jeffThompson/VibrationInterface/ProcessPhotos/2ChannelVibeBoard_Back.jpg

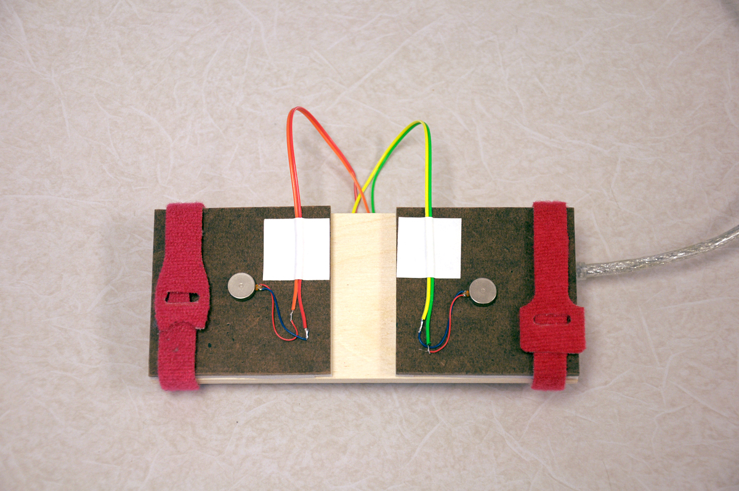
ProcessPhotos/2ChannelVibeBoard_Back.jpg
