jeffThompson/VibrationInterface/ProcessPhotos/2ChannelVibeBoard_Front.jpg

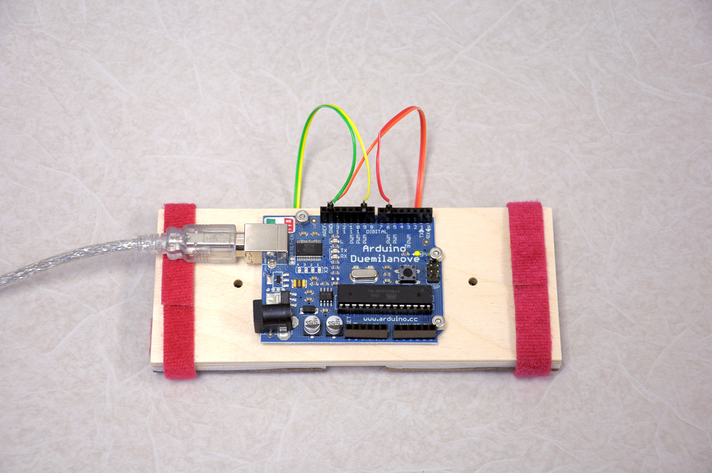
ProcessPhotos/2ChannelVibeBoard_Front.jpg
