jeffThompson/VibrationInterface/ProcessPhotos/2dArrayGeneration_Arduino-web.png

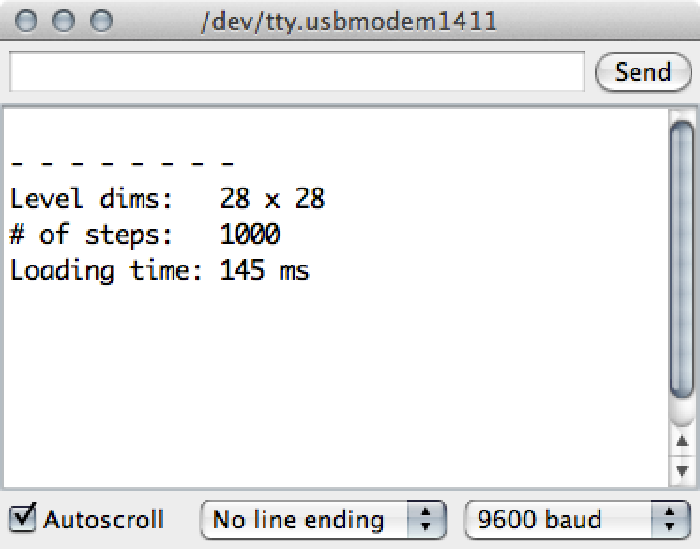
ProcessPhotos/2dArrayGeneration_Arduino-web.png
