jeffThompson/VibrationInterface/ProcessPhotos/Black1-4inBoard.jpg

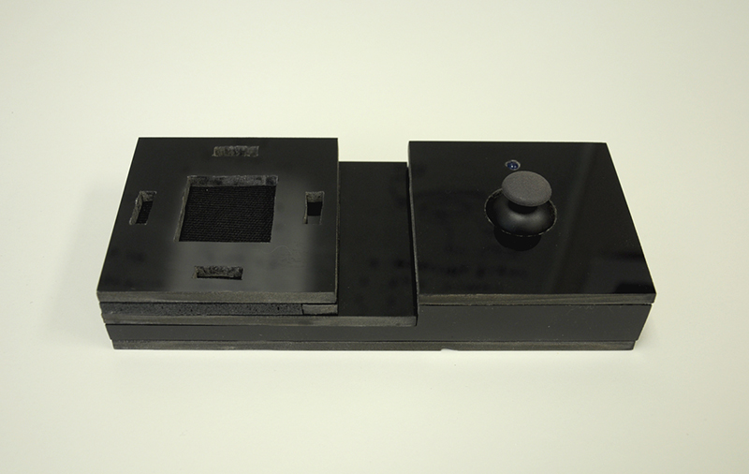
ProcessPhotos/Black1-4inBoard.jpg
