jeffThompson/VibrationInterface/ProcessPhotos/Board_v0.9Bottom.png

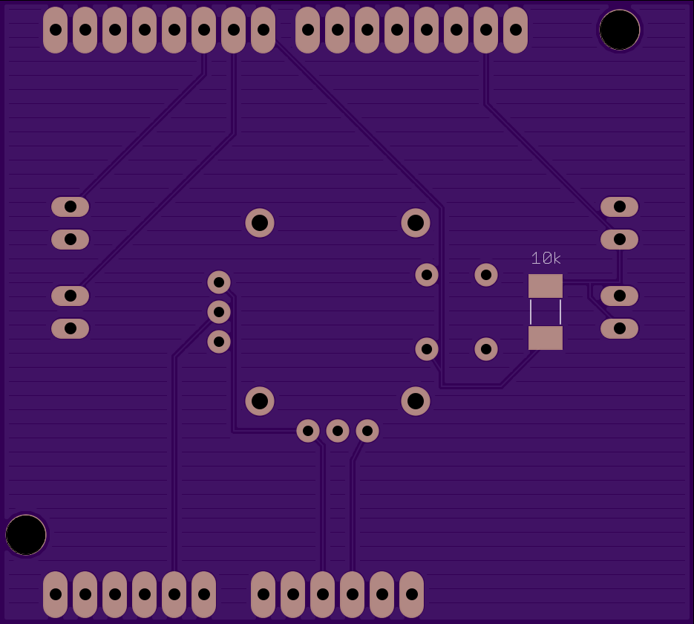
ProcessPhotos/Board_v0.9Bottom.png
