jeffThompson/VibrationInterface/ProcessPhotos/Board_v0.9Top.png

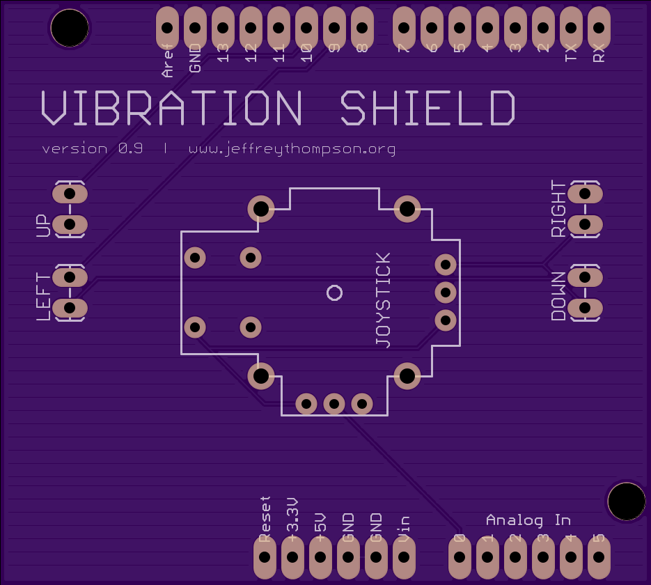
ProcessPhotos/Board_v0.9Top.png
