jeffThompson/VibrationInterface/ProcessPhotos/DistillingOils_01.jpg

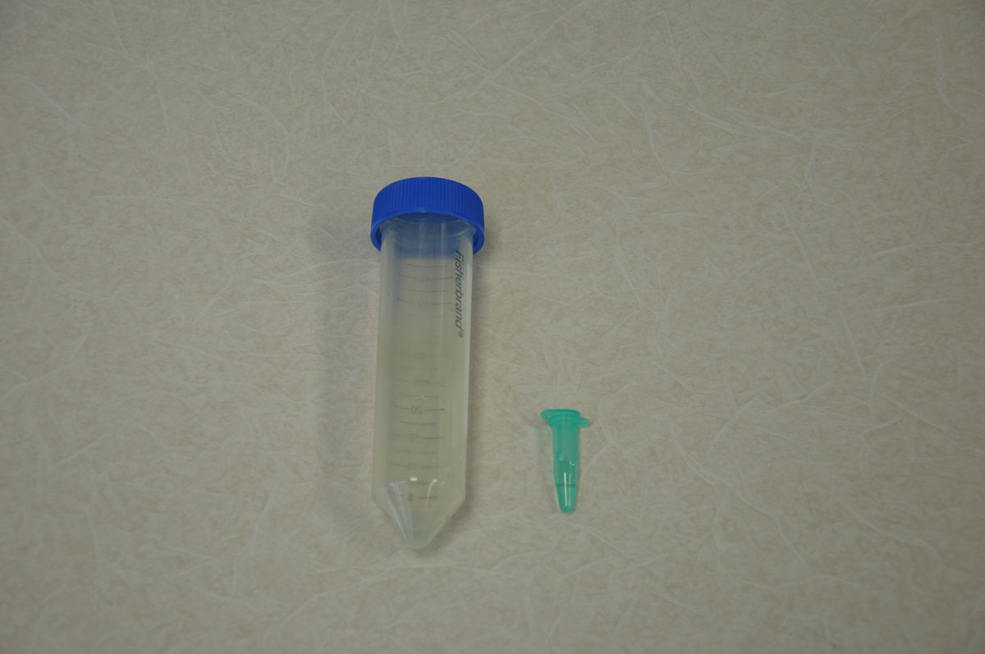
ProcessPhotos/DistillingOils_01.jpg
