jeffThompson/VibrationInterface/ProcessPhotos/DistillingOils_02.jpg

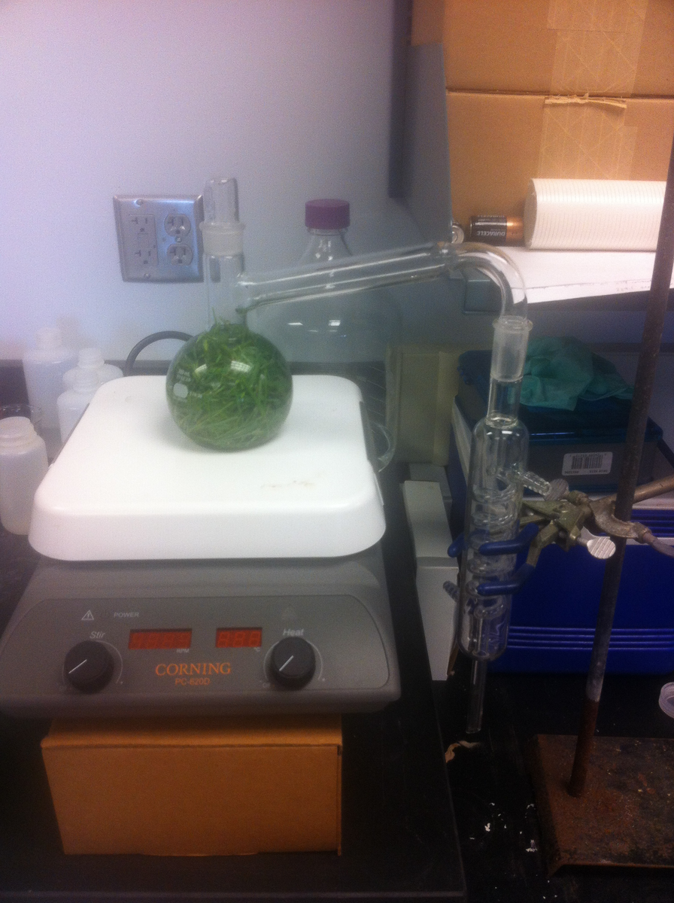
ProcessPhotos/DistillingOils_02.jpg
