jeffThompson/VibrationInterface/ProcessPhotos/DistillingOils_03.jpg

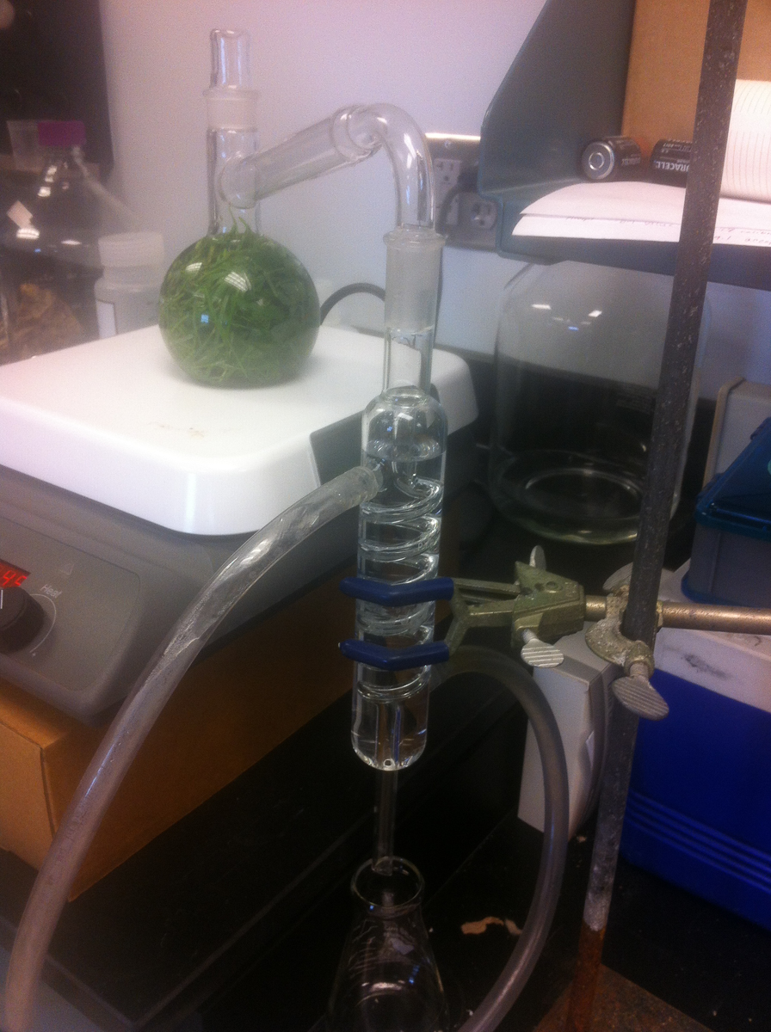
ProcessPhotos/DistillingOils_03.jpg
