jeffThompson/VibrationInterface/ProcessPhotos/DistillingOils_04.jpg

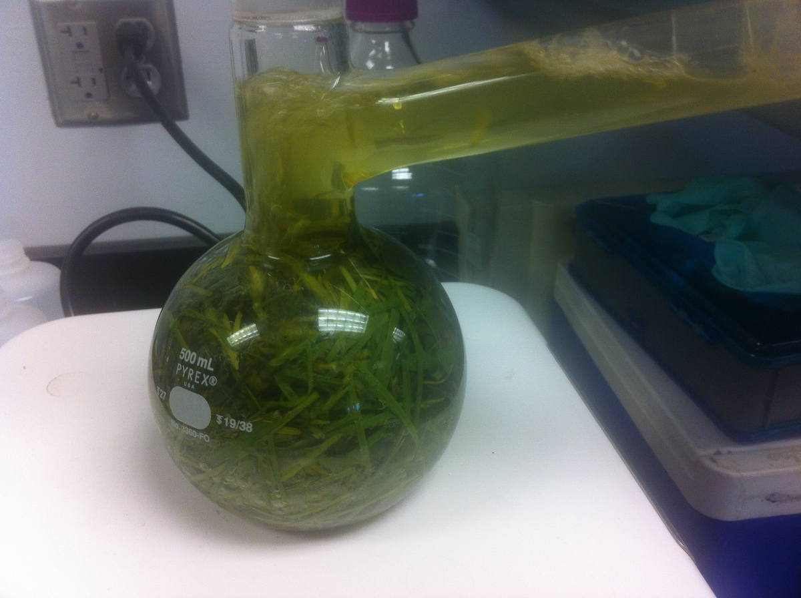
ProcessPhotos/DistillingOils_04.jpg
