jeffThompson/VibrationInterface/ProcessPhotos/DistillingOils_05.jpg

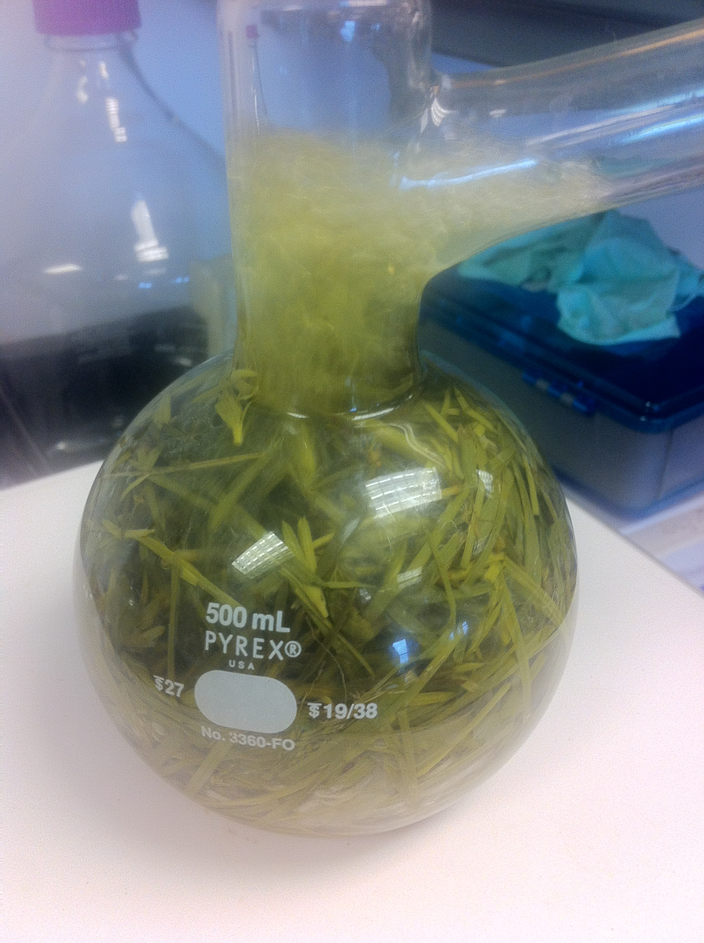
ProcessPhotos/DistillingOils_05.jpg
