jeffThompson/VibrationInterface/ProcessPhotos/DistillingOils_06.jpg

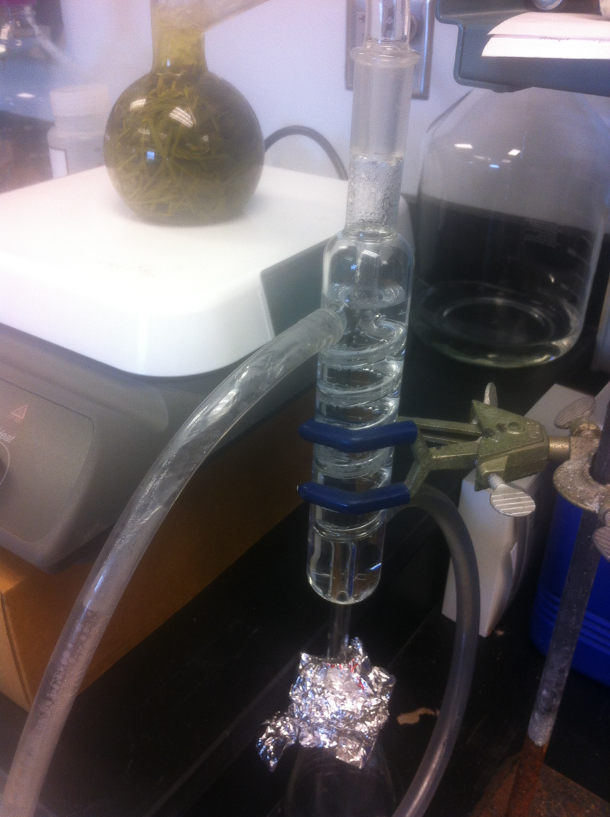
ProcessPhotos/DistillingOils_06.jpg
