jeffThompson/VibrationInterface/ProcessPhotos/DistillingOils_07.jpg

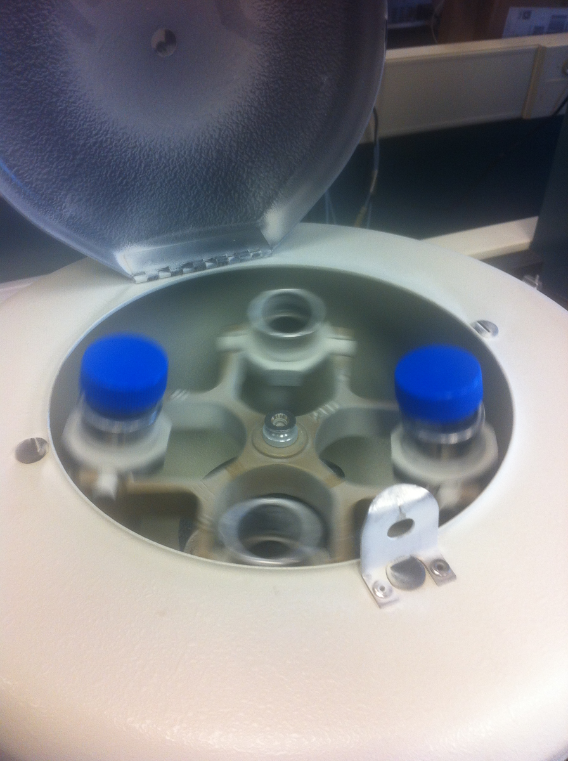
ProcessPhotos/DistillingOils_07.jpg
