jeffThompson/VibrationInterface/ProcessPhotos/EarlyVibrationInterface.jpg

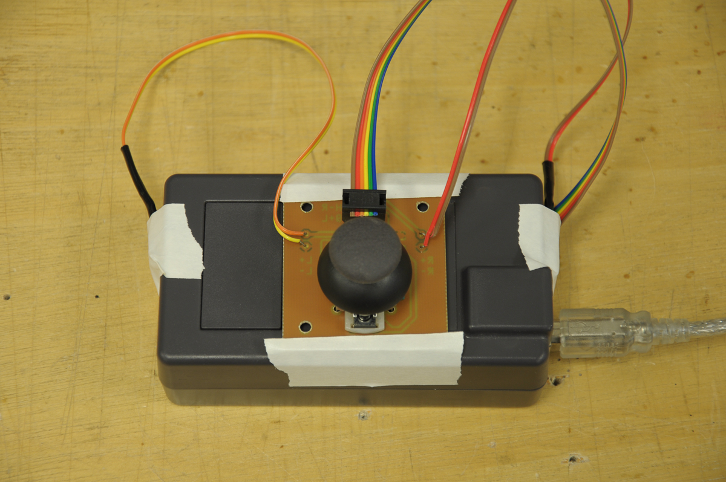
ProcessPhotos/EarlyVibrationInterface.jpg
