jeffThompson/VibrationInterface/ProcessPhotos/Final3dModel_Top.png

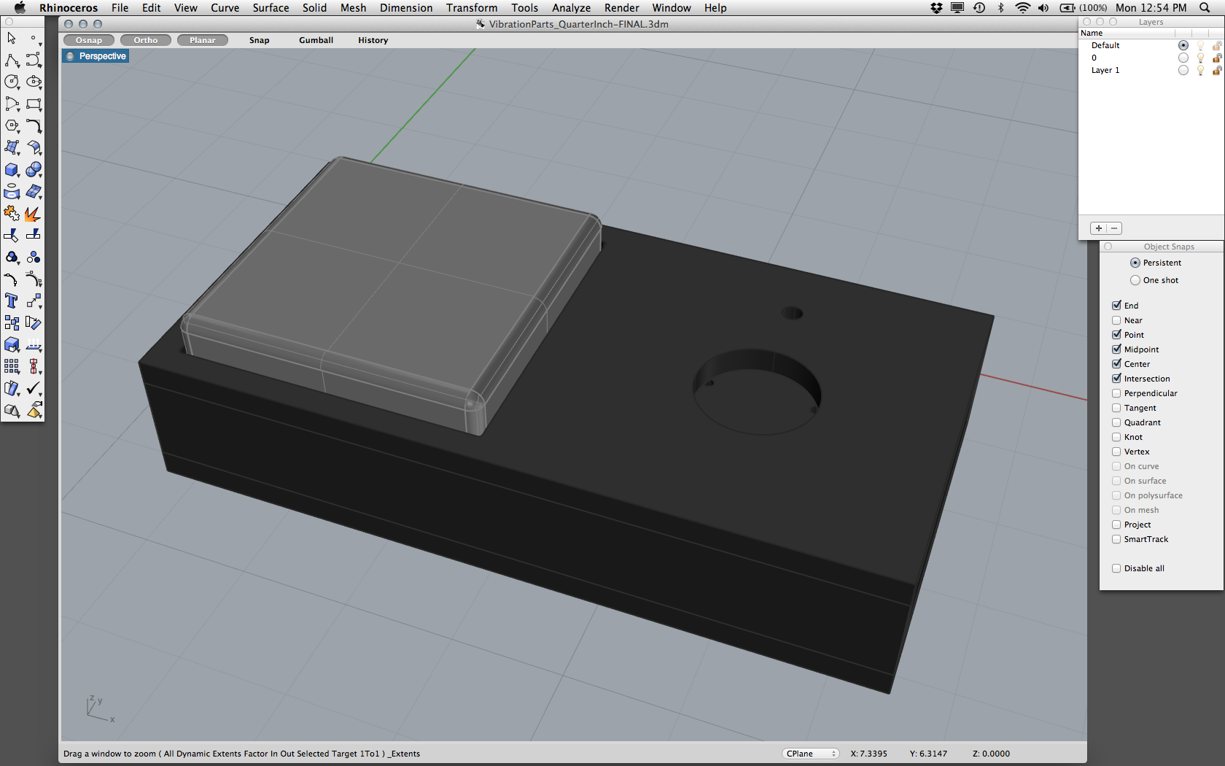
ProcessPhotos/Final3dModel_Top.png
