jeffThompson/VibrationInterface/ProcessPhotos/LasercutFelt-web.png

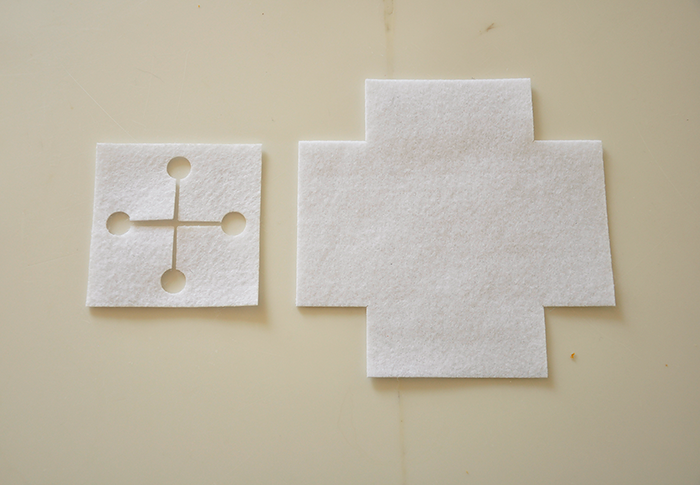
ProcessPhotos/LasercutFelt-web.png
