jeffThompson/VibrationInterface/ProcessPhotos/LasercutFelt.jpg

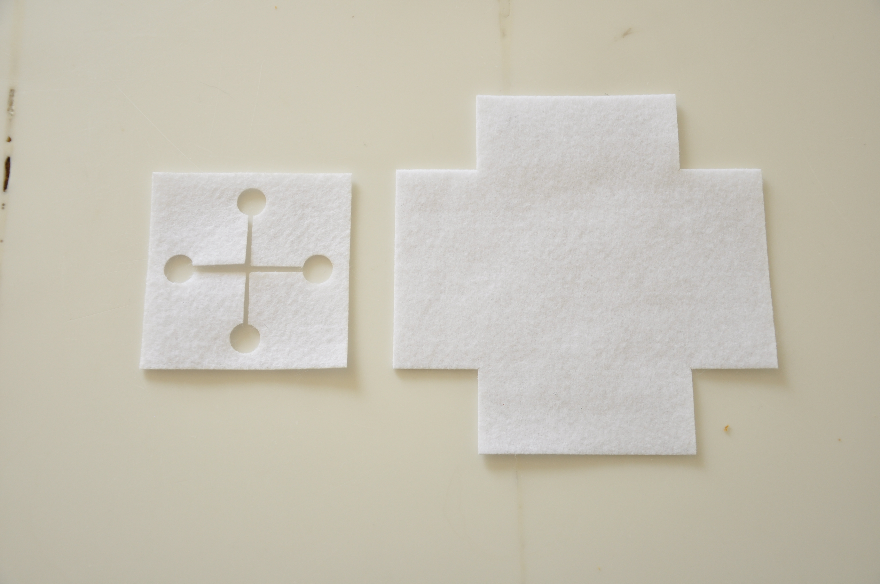
ProcessPhotos/LasercutFelt.jpg
