jeffThompson/VibrationInterface/ProcessPhotos/PCB_Bottom.png

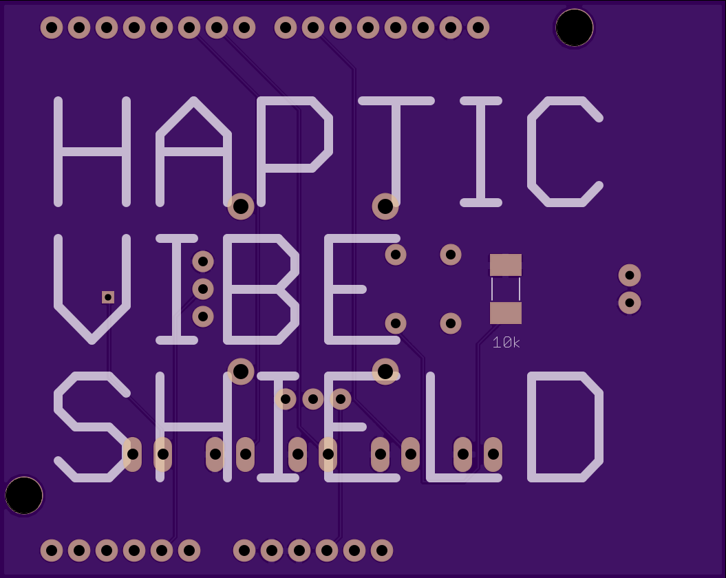
ProcessPhotos/PCB_Bottom.png
