jeffThompson/VibrationInterface/ProcessPhotos/PCB_Top.png

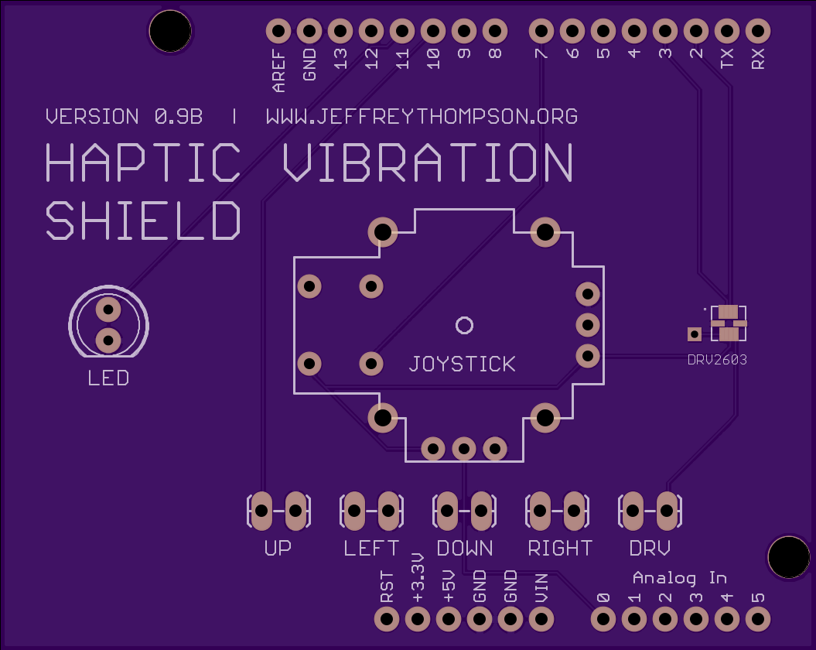
ProcessPhotos/PCB_Top.png
