jeffThompson/VibrationInterface/ProcessPhotos/TinyDogboneCornersOfVibrationBoardModel.png

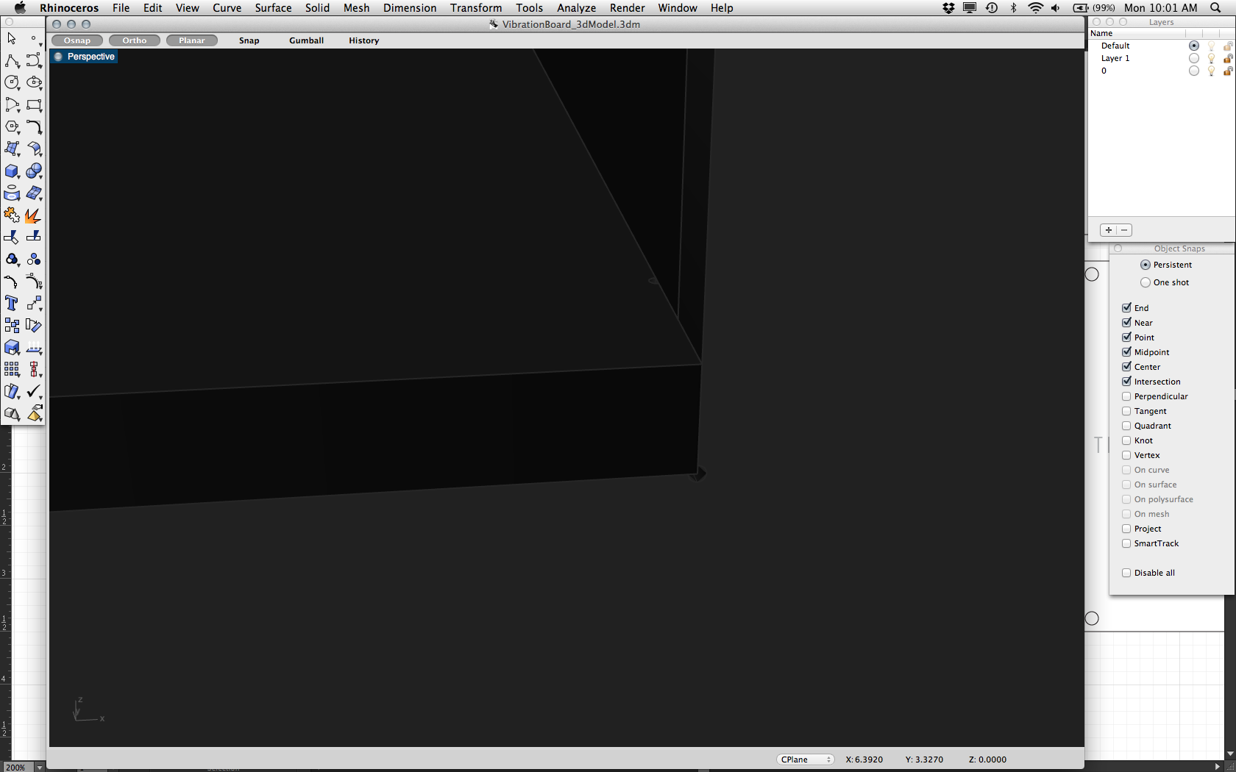
ProcessPhotos/TinyDogboneCornersOfVibrationBoardModel.png
