jeffThompson/VibrationInterface/ProcessPhotos/VibrationBoard_3dModel.png

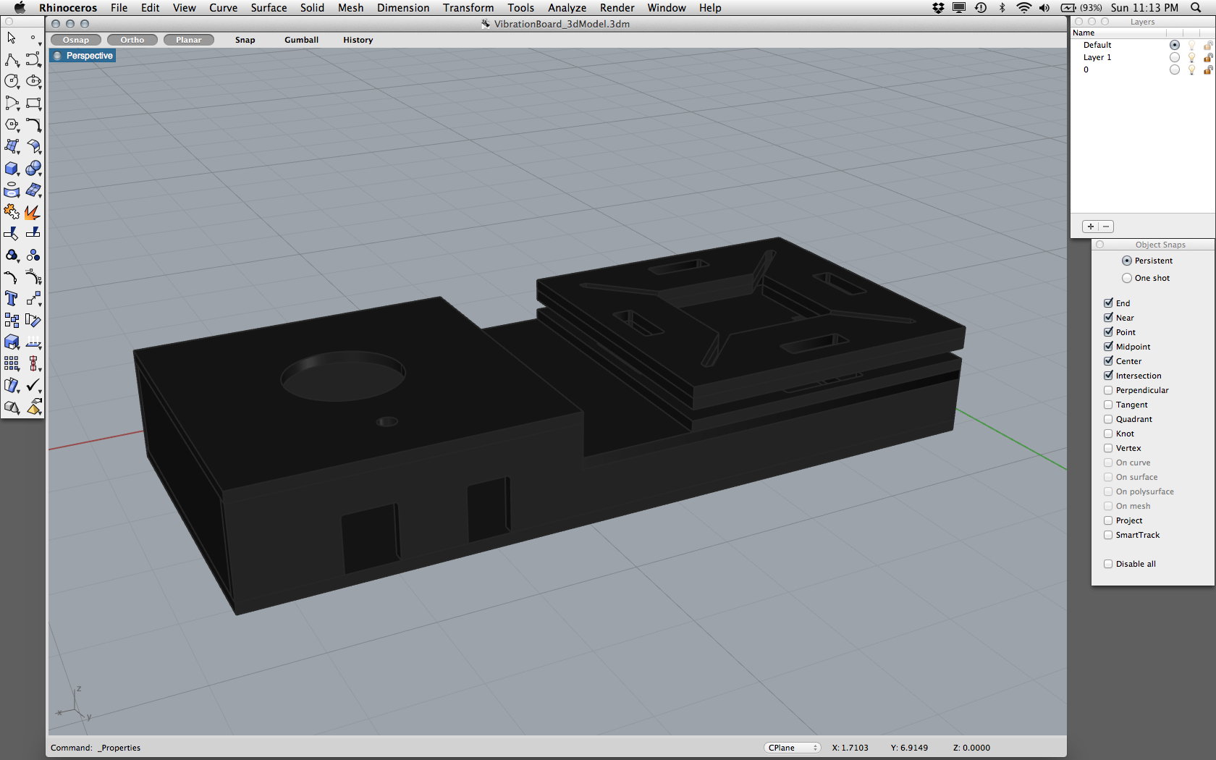
ProcessPhotos/VibrationBoard_3dModel.png
