jeffThompson/VibrationInterface/ProcessPhotos/VibrationShield_v0-9.jpg

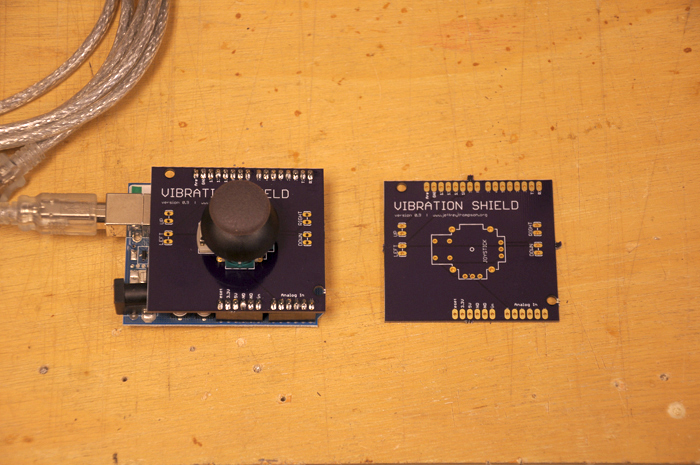
ProcessPhotos/VibrationShield_v0-9.jpg
