jeffThompson/VibrationInterface/ProcessPhotos/ScentImpregnationTest-01.jpg

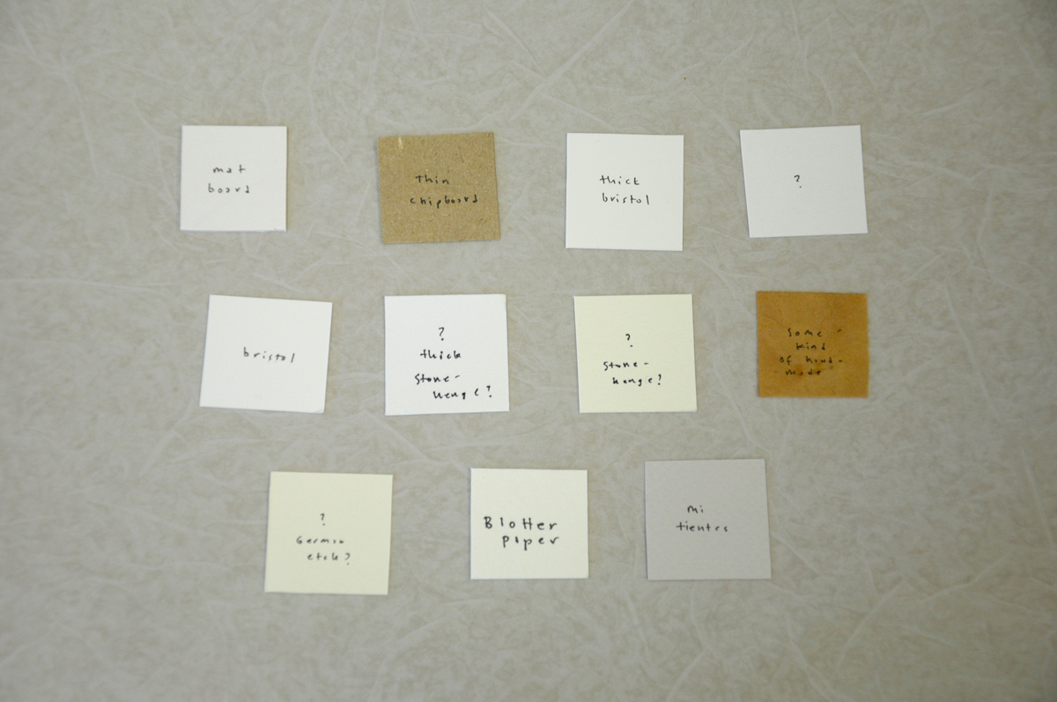
ProcessPhotos/ScentImpregnationTest-01.jpg
